mike-rankin/ESP32_Desktop_Clock/Images/Image1.jpg

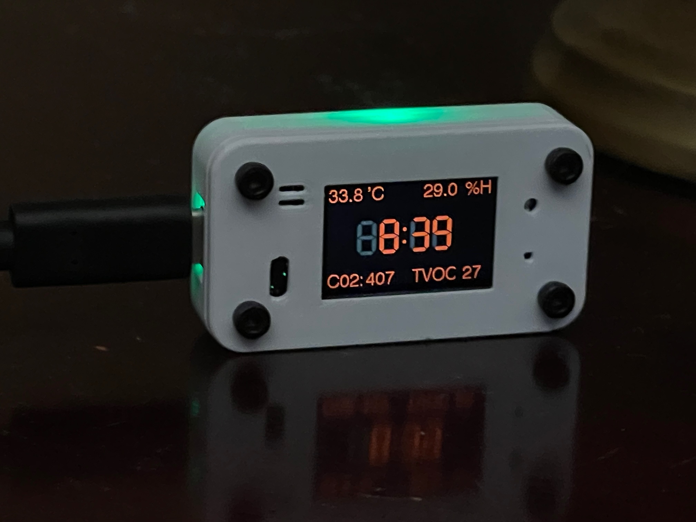
Images/Image1.jpg
