mike-rankin/ESP32_Desktop_Clock/Images/Image2.jpg

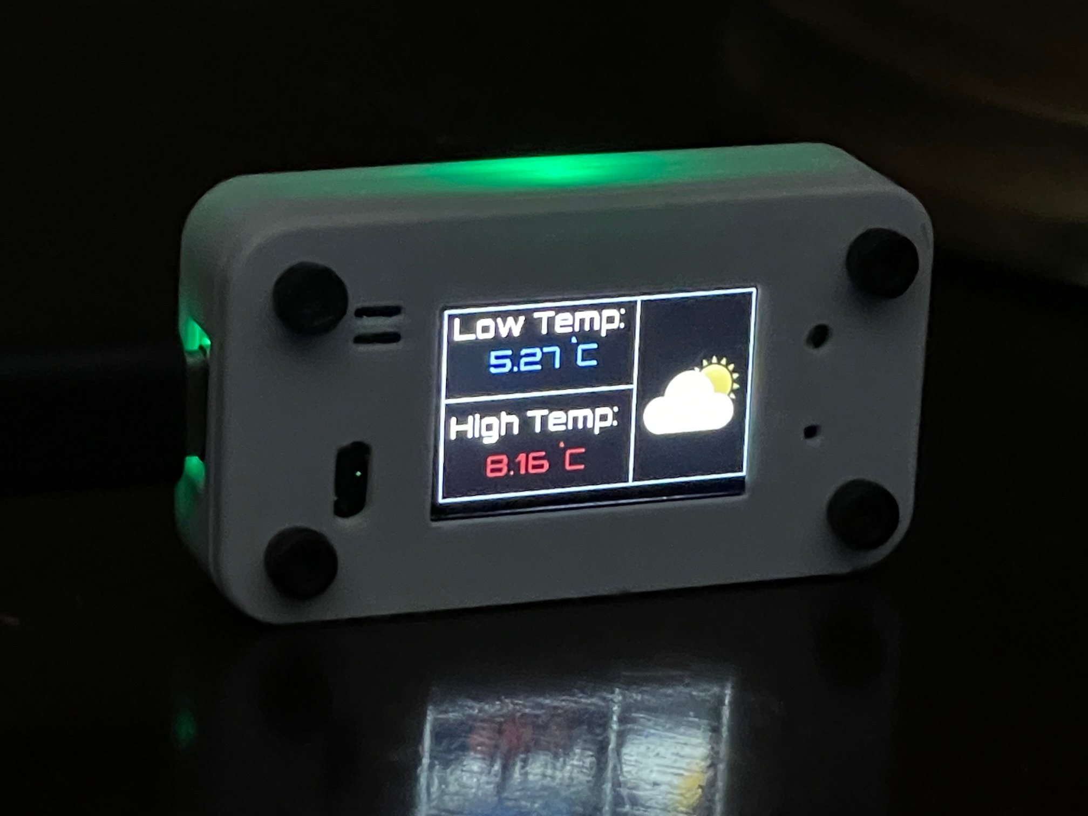
Images/Image2.jpg
