mike-rankin/ESP32_Desktop_Clock/Images/IMG_1357.jpg

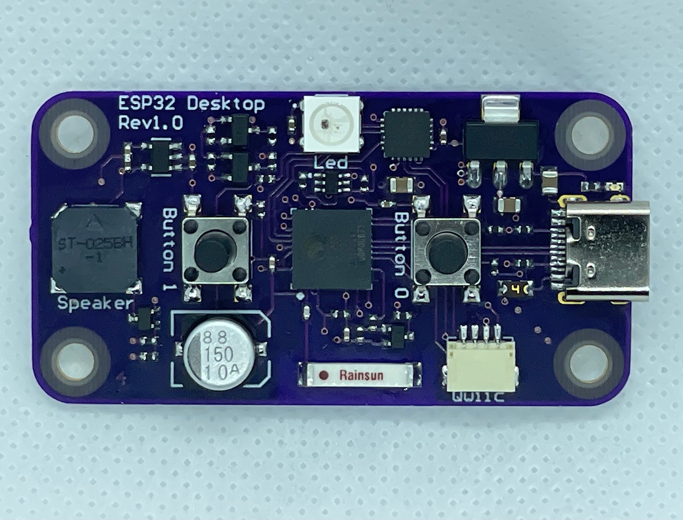
Images/IMG_1357.jpg
