mike-rankin/ESP32_Desktop_Clock/Images/IMG_1358.jpg

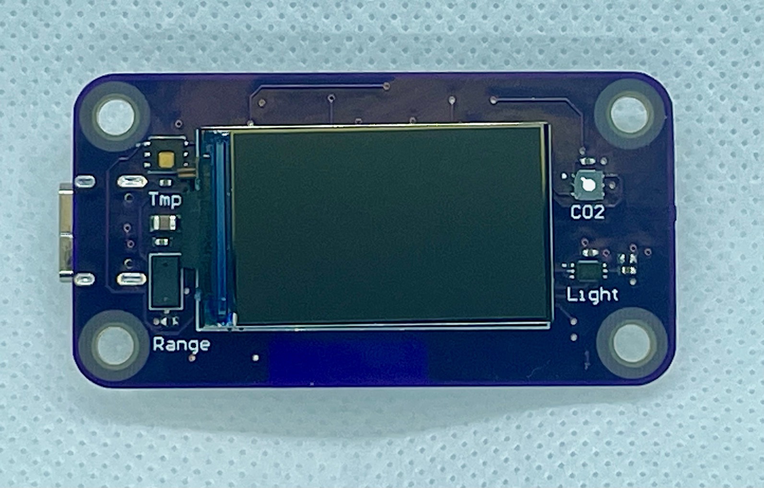
Images/IMG_1358.jpg
