mike-rankin/ESP32_Desktop_Clock/Code/Desktop_Clock/icons.h

//Great Example of weather data formatting: https://github.com/xxlukas42/SensorlessWeatherStation/blob/master/sensorless_weather_station.ino
//Create C arrays from jpeg images using this online tool:
//    http://tomeko.net/online_tools/file_to_hex.php?lang=en


/*  Create C arrays from jpeg images using this online tool:
    http://tomeko.net/online_tools/file_to_hex.php?lang=en

    If needed, first resize and crop to an appropriate width and height
    to suit your display with an image editting program such as IrfanView.
    
    You can also change the image "guality" to reduce the file size.
    
    Paste the array into a new tabe, top and tail the array from the
    tool to look like the one below with:

    #include <pgmspace.h>
    const uint8_t name[] PROGMEM = {

    to start and and end with:

   };

    Change the name of the array. Make sure the original jpeg is less than 32Kbyes
    as there is an array size limit imposed by the Arduino IDE!


*/

#include <pgmspace.h>
const uint8_t sun[] PROGMEM = 
{

 0xFF, 0xD8, 0xFF, 0xE0, 0x00, 0x10, 0x4A, 0x46, 0x49, 0x46, 0x00, 0x01, 0x01, 0x01, 0x00, 0xC0, 
0x00, 0xC0, 0x00, 0x00, 0xFF, 0xE1, 0x00, 0x22, 0x45, 0x78, 0x69, 0x66, 0x00, 0x00, 0x4D, 0x4D, 
0x00, 0x2A, 0x00, 0x00, 0x00, 0x08, 0x00, 0x01, 0x01, 0x12, 0x00, 0x03, 0x00, 0x00, 0x00, 0x01, 
0x00, 0x01, 0x00, 0x00, 0x00, 0x00, 0x00, 0x00, 0xFF, 0xDB, 0x00, 0x43, 0x00, 0x02, 0x01, 0x01, 
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
0xA3, 0xA4, 0xA5, 0xA6, 0xA7, 0xA8, 0xA9, 0xAA, 0xB2, 0xB3, 0xB4, 0xB5, 0xB6, 0xB7, 0xB8, 0xB9, 
0xBA, 0xC2, 0xC3, 0xC4, 0xC5, 0xC6, 0xC7, 0xC8, 0xC9, 0xCA, 0xD2, 0xD3, 0xD4, 0xD5, 0xD6, 0xD7, 
0xD8, 0xD9, 0xDA, 0xE2, 0xE3, 0xE4, 0xE5, 0xE6, 0xE7, 0xE8, 0xE9, 0xEA, 0xF2, 0xF3, 0xF4, 0xF5, 
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

};
