mike-rankin/ESP32_Desktop_Clock/Code/Desktop_Clock/Orbitron_Medium_20.h

// Created by http://oleddisplay.squix.ch/ Consider a donation
// In case of problems make sure that you are using the font file with the correct version!
const uint8_t Orbitron_Medium_20Bitmaps[] PROGMEM = {

	// Bitmap Data:
	0x00, // ' '
	0xDB,0x6D,0xB6,0xD8,0x0D,0x80, // '!'
	0xDB,0x6D,0x80, // '"'
	0x06,0x1C,0x1C,0x30,0x30,0x67,0xFF,0xEF,0xFF,0xC3,0x06,0x06,0x18,0x1C,0x30,0x30,0x61,0xFF,0xFB,0xFF,0xF3,0x06,0x06,0x1C,0x1C,0x30,0x00, // '#'
	0x03,0x00,0x06,0x00,0x0C,0x07,0xFF,0xCF,0xFF,0xD8,0x61,0xB0,0xC0,0x61,0x80,0xC3,0x01,0xFF,0xF1,0xFF,0xF0,0x18,0x60,0x30,0xC0,0x61,0xB0,0xC3,0x7F,0xFE,0x7F,0xF8,0x06,0x00,0x0C,0x00, // '$'
	0x7C,0x01,0x31,0x81,0xCC,0x60,0xF3,0x18,0x70,0xC6,0x38,0x1F,0x1C,0x00,0x0E,0x00,0x0F,0x3C,0x07,0x1F,0x83,0x8C,0x21,0xC3,0x08,0xE0,0xC2,0x30,0x1F,0x88,0x07,0xC0, // '%'
	0x7F,0xF8,0x1F,0xFF,0x06,0x00,0xC1,0x80,0x00,0x60,0x00,0x1C,0x00,0x0F,0xC0,0x03,0x3C,0x30,0xC3,0xCC,0x30,0x3F,0x0C,0x03,0xE3,0x00,0x3C,0xFF,0xFF,0x9F,0xFE,0x20, // '&'
	0xDB,0x00, // '''
	0x6E,0xCC,0xCC,0xCC,0xCC,0xCC,0xE6, // '('
	0xE7,0x1C,0xE7,0x39,0xCE,0x73,0x9C,0xEE,0x60, // ')'
	0x18,0x0C,0x3F,0xDF,0xE3,0xC3,0xE1,0xB8,0x48, // '*'
	0x18,0x0C,0x06,0x1F,0xEF,0xF0,0xC0,0x60,0x30, // '+'
	0xDB,0x68, // ','
	0xFF,0x7F,0x80, // '-'
	0xD8, // '.'
	0x00,0x40,0x18,0x03,0x00,0xC0,0x30,0x0E,0x03,0x80,0xE0,0x18,0x06,0x01,0x80,0x70,0x0C,0x01,0x00,0x00, // '/'
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
	  {   430,  15,  14,  18,    1,  -14 }, // '9'
	  {   457,   3,  12,   5,    1,  -12 }, // ':'
	  {   462,   3,  15,   5,    1,  -12 }, // ';'
	  {   468,   9,  12,  10,    0,  -12 }, // '<'
	  {   482,  12,   6,  14,    1,   -9 }, // '='
	  {   491,   9,  12,  11,    1,  -12 }, // '>'
	  {   505,  13,  14,  15,    1,  -14 }, // '?'
	  {   528,  16,  14,  18,    1,  -14 }, // '@'
	  {   556,  16,  14,  18,    1,  -14 }, // 'A'
	  {   584,  16,  14,  18,    1,  -14 }, // 'B'
	  {   612,  15,  14,  17,    1,  -14 }, // 'C'
	  {   639,  16,  14,  18,    1,  -14 }, // 'D'
	  {   667,  14,  14,  16,    1,  -14 }, // 'E'
	  {   692,  14,  14,  15,    1,  -14 }, // 'F'
	  {   717,  16,  14,  18,    1,  -14 }, // 'G'
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
};

const GFXfont Orbitron_Medium_20 PROGMEM = {
(uint8_t  *)Orbitron_Medium_20Bitmaps,(GFXglyph *)Orbitron_Medium_20Glyphs,0x20, 0x7E, 20};
